Esdrin/SmartClock/Assets/image-20240804144859555.png

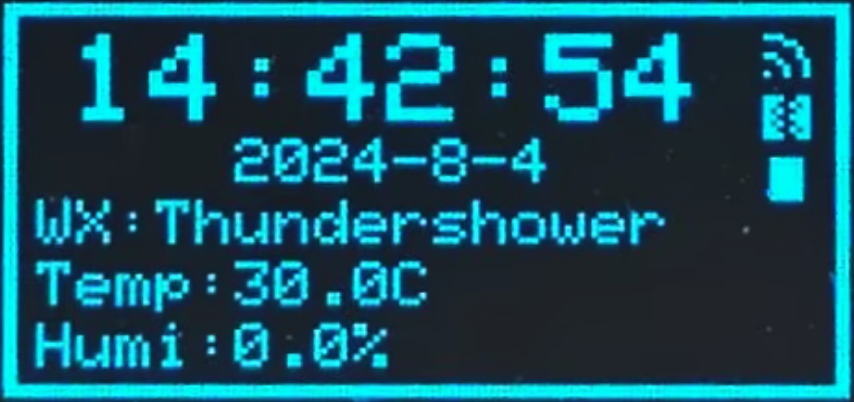
Assets/image-20240804144859555.png
