Esdrin/SmartClock/OrderFile/Model/BottomShell.STEP

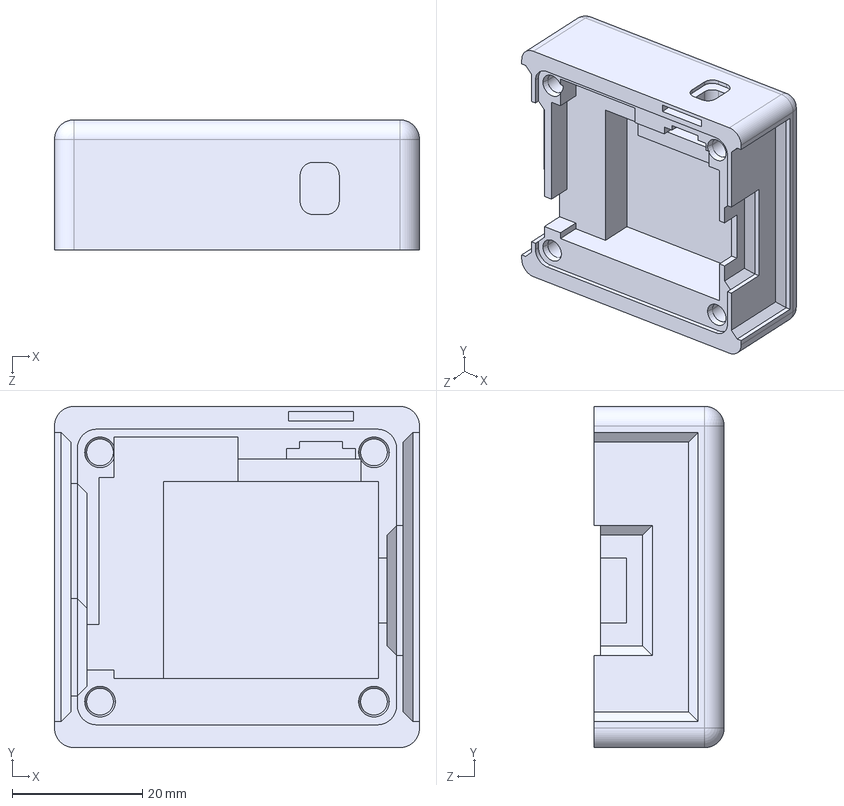
[picture p9: CAD file, 2024-08-04]
OrderFile/Model/BottomShell.STEP
56.0 x 52.4 x 20.0 mm
