Esdrin/SmartClock/OrderFile/Model/TopShell.STEP

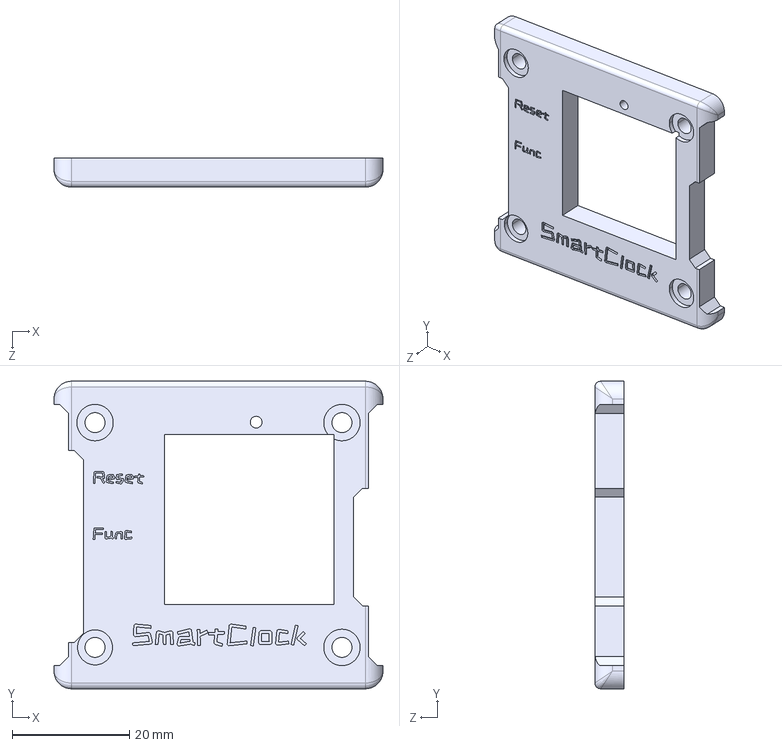
[picture p10: CAD file, 2024-08-04]
OrderFile/Model/TopShell.STEP
56.0 x 52.4 x 5.00 mm
