Esdrin/SmartClock/Model/TopShell.SLDPRT

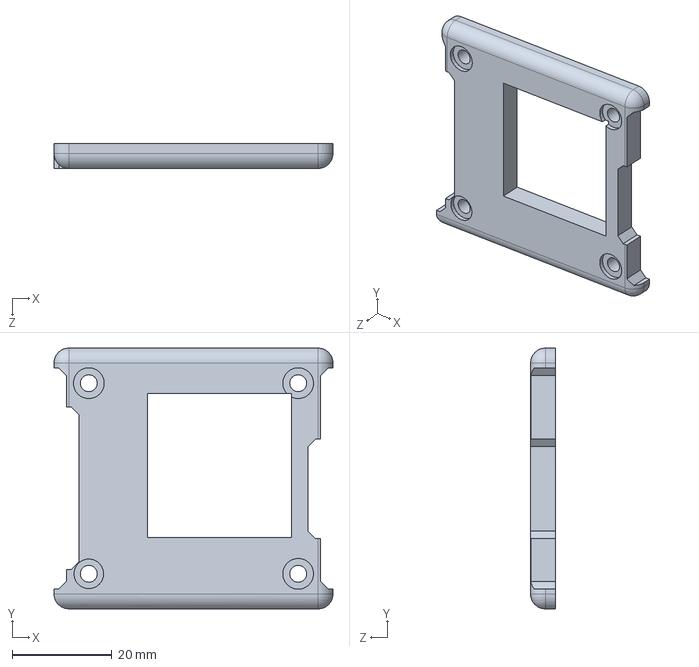
[picture p11: CAD file, 2024-08-04]
Model/TopShell.SLDPRT
56.0 x 52.4 x 5.00 mm
