Esdrin/SmartClock/Model/PCB_Node/5Jub-U9.SLDASM

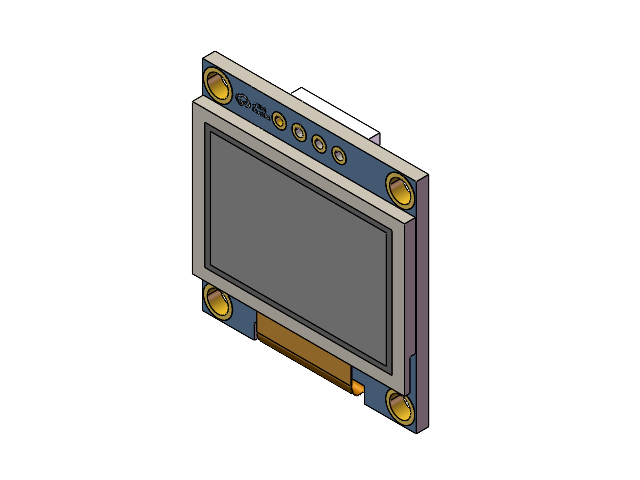
[picture p13: CAD file, 2024-08-04]
Model/PCB_Node/5Jub-U9.SLDASM
零件1^5Jub-U9
